resilient-arch-lab/BitCrusher/interface/src/device/comms.py

"""

"""

import serial
from dataclasses import dataclass
from enum import Enum

class Headers(Enum):
    # error checking responses (returned from device)
    # body of responses used to return any necessary values to commands sent from host
    success = b"\x01"
    error = b"\x02"

    # set global device parameters (sent from host)
    get_param = b"\x11"
    set_param = b"\x12"

    # get device state (sent from host)
    get_state = b"\x21"

    # arming / disarming commands 
    arm = b"\xa0"
    set_arm_param = b"\xa1"
    get_arm_param = b"\xa2"
    disarm = b"\xaf"

    # debugging headers
    debug = b"\xd0"

# The BitCrusher UART protocol
class Protocol:
    Headers = Headers
    
    @dataclass(frozen=True)
    class Message:
        hdr: Headers
        body: bytes

    # some other property definitions
    body_max_len: int = 256

    @classmethod
    def parse_from_bytes(cls, hdr: bytes, body: bytes) -> Message:
        try:
            hdr_val = cls.Headers(hdr)
        except KeyError as e:
            e.add_note(f"Failed to parse message: \"{hex(int(hdr))}\" is invalid header")
            raise e

        return cls.Message(hdr_val, body)
    
    @staticmethod
    def to_bytes(msg: Message) -> bytes:
        hdr = msg.hdr.value
        body = msg.body
        out = hdr + len(body).to_bytes(1) + body
        return out
